aeberbach/A1200KB/3Dfiles/Original Amiga case/rev4/Base.SLDPRT

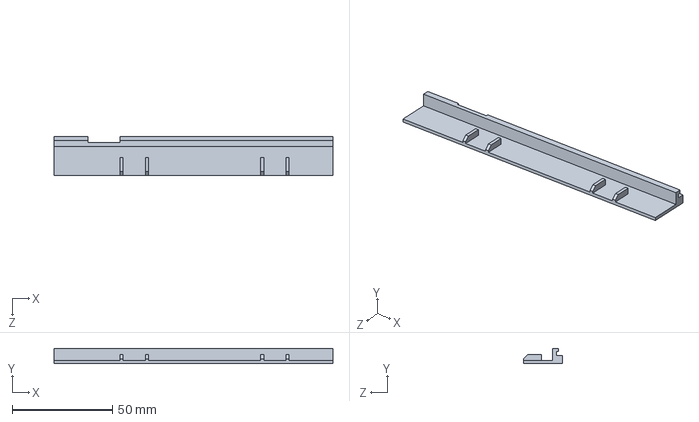
[picture p19: CAD file, 2021-08-29]
3Dfiles/Original Amiga case/rev4/Base.SLDPRT
139.0 x 7.35 x 19.5 mm
