aeberbach/A1200KB/3Dfiles/A1200.net case/Right side.stl

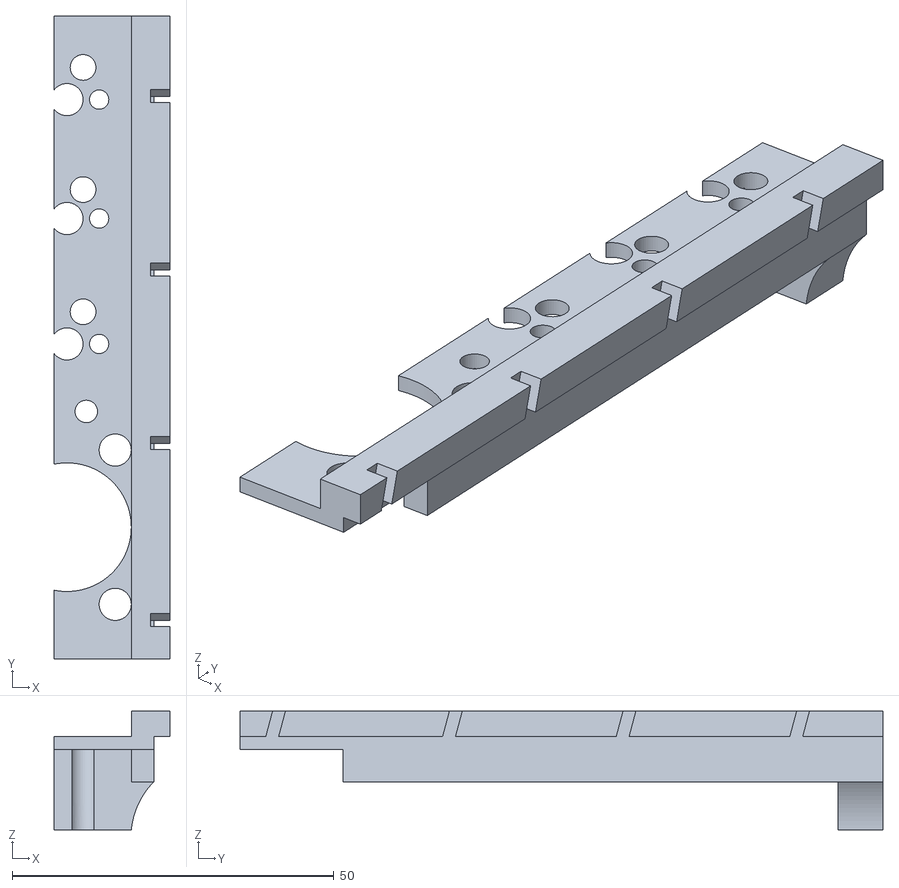
[picture p20: CAD file, 2020-05-30]
3Dfiles/A1200.net case/Right side.stl
18.0 x 100.0 x 18.5
