aeberbach/A1200KB/created/A1200KB.kicad_pcb

## KiCad design hw/mouse.sch

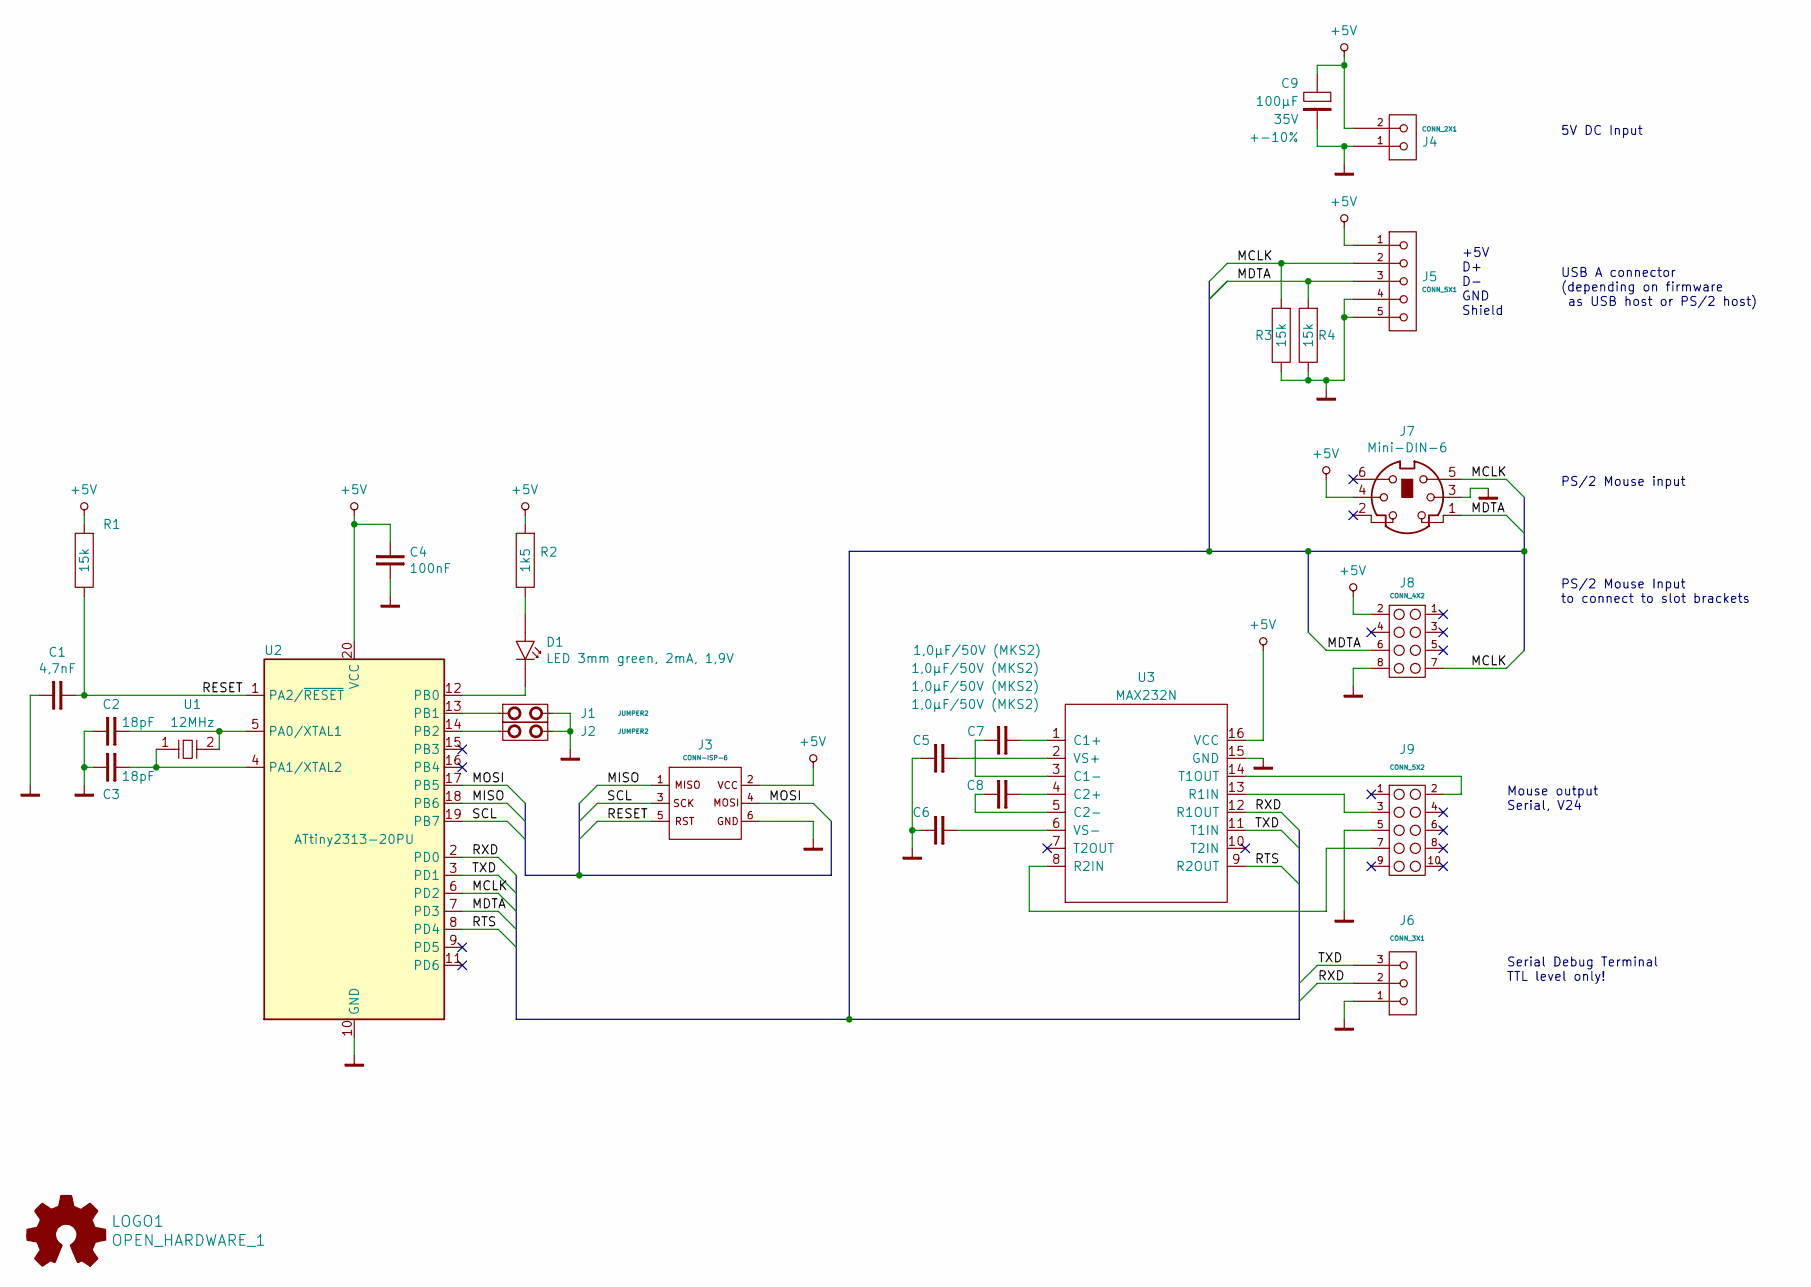
[picture p25: schematic mouse.sch]

Parts:
C1: 4,7nF; C_RM5.08mm_5x5mm
C2, C3: 18pF; C_CER_2.54mm
C4: 100nF; C_RM5.08mm_5x2.5mm
C5, C6, C7, C8: 1,0µF/50V (MKS2); C_RM5.08mm_5x5mm
C9: 100µF; CP_RM2.54mm_D6.5mm; Voltage 35V
D1: LED 3mm green, 2mA, 1,9V; LED_RM2.54mm_D3mm
J1, J2: JUMPER2; HEADER_2x1
J3: CONN-ISP-6; HEADER_3x2
J4: CONN_2X1; PCB_CON2
J5: CONN_5X1; USB_A
J6: CONN_3X1; HEADER_3x1
J7: Mini-DIN-6
J8: CONN_4X2; HEADER_4x2
J9: CONN_5X2; HEADER_5x2
LOGO1: OPEN_HARDWARE_1; Symbol_OSHW-Logo_Copper
R1, R3, R4: 15k; R_RM10.16mm
R2: 1k5; R_RM10.16mm
U1: 12MHz; CRY_HC49
U2: ATtiny2313-20PU; DIP-20_W7.62mm
U3: MAX232N; DIP16

Connections:
+5V: C4.1, C9.1, J3.2, J4.2, J5.1, J7.4, J8.2, R1.1, R2.1, U2.20 (VCC), U3.16 (VCC)
GND: C1.1, C2.1, C3.1, C4.2, C5.1, C6.1, C9.2, J1.2, J2.2, J3.6, J4.1, J5.4, J5.5, J6.1, J7.3, J8.8, J9.5, R3.2, R4.2, U2.10 (GND), U3.15 (GND)
MCLK: J5.2, J7.5, J8.7, R3.1, U2.6 (PD2)
MDTA: J5.3, J7.1, J8.6, R4.1, U2.7 (PD3)
MISO: J3.1, U2.18 (PB6)
MOSI: J3.4, U2.17 (PB5)
unnamed: C2.2, U1.2, U2.5 (PA0/XTAL1)
unnamed: C3.2, U1.1, U2.4 (PA1/XTAL2)
unnamed: C5.2, U3.2 (VS+)
unnamed: C6.2, U3.6 (VS-)
unnamed: C7.1, U3.3 (C1-)
unnamed: C7.2, U3.1 (C1+)
unnamed: C8.1, U3.4 (C2+)
unnamed: C8.2, U3.5 (C2-)
unnamed: D1.1 (A), R2.2
unnamed: D1.2 (C), U2.12 (PB0)
unnamed: J1.1, U2.13 (PB1)
unnamed: J2.1, U2.14 (PB2)
unnamed: J9.2, U3.14 (T1OUT)
unnamed: J9.3, U3.13 (R1IN)
unnamed: J9.7, U3.8 (R2IN)
RESET: C1.2, J3.5, R1.2, U2.1 (PA2/~RESET)
RTS: U2.8 (PD4), U3.9 (R2OUT)
RXD: J6.2, U2.2 (PD0), U3.12 (R1OUT)
SCL: J3.3, U2.19 (PB7)
TXD: J6.3, U2.3 (PD1), U3.11 (T1IN)

Notes on the sheet:
Serial Debug Terminal TTL level only!
Mouse output Serial, V24
PS/2 Mouse input
PS/2 Mouse Input to connect to slot brackets
5V DC Input
+5V D+ D- GND Shield
USB A connector (depending on firmware as USB host or PS/2 host)
